Shihara1020/e21-3yp-SlideSense-Project/docs/images/e21452.jpg

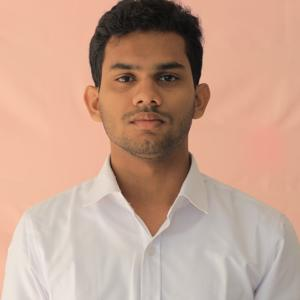
docs/images/e21452.jpg
