Shihara1020/e21-3yp-SlideSense-Project/docs/images/TechStack2.png

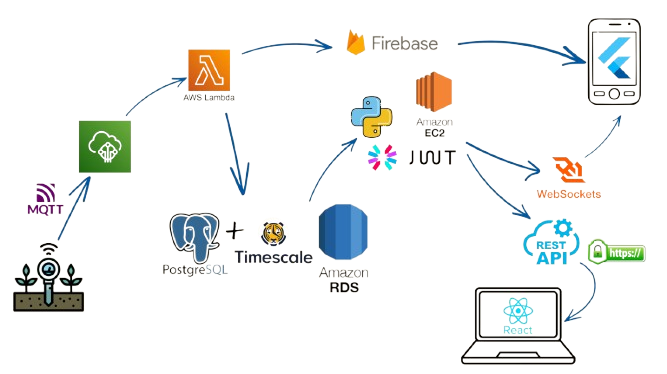
docs/images/TechStack2.png
