Shihara1020/e21-3yp-SlideSense-Project/docs/images/TechStack.png

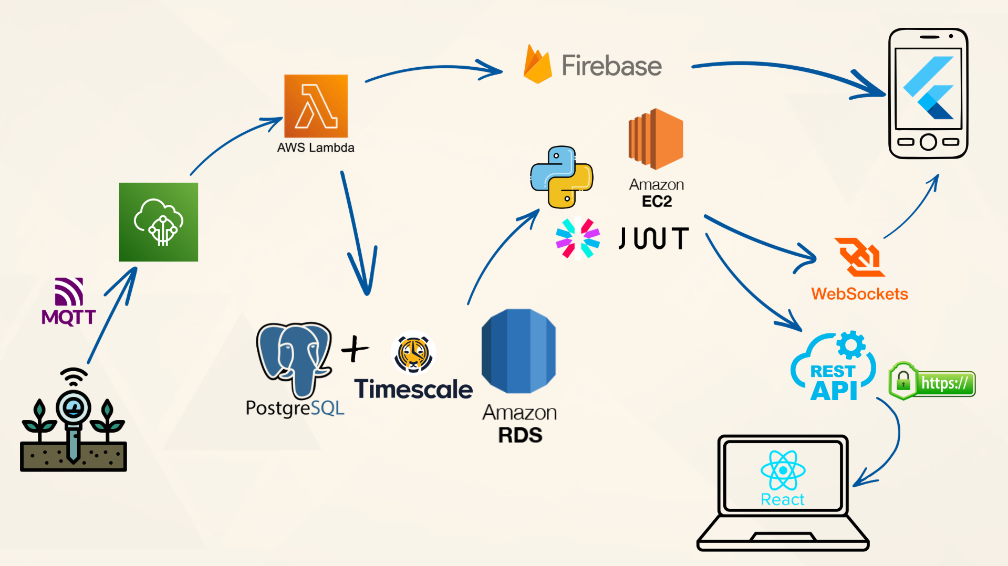
docs/images/TechStack.png
