Shihara1020/e21-3yp-SlideSense-Project/docs/images/yasodha-vimukthi.jpeg

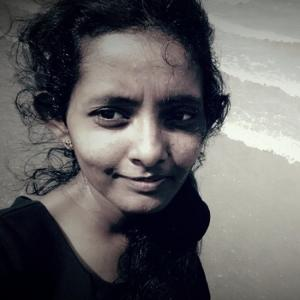
docs/images/yasodha-vimukthi.jpeg
