Shihara1020/e21-3yp-SlideSense-Project/ESP32_Scripts/ESP32_External_Power.png

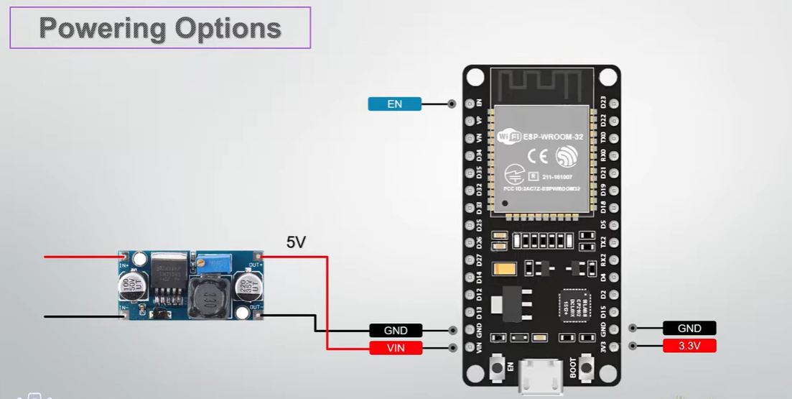
ESP32_Scripts/ESP32_External_Power.png
