Shihara1020/e21-3yp-SlideSense-Project/ESP32_Scripts/ESP32_Pin_Digram.png

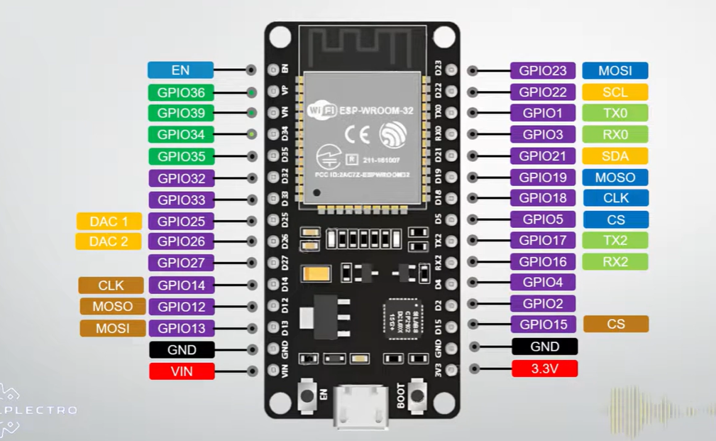
ESP32_Scripts/ESP32_Pin_Digram.png
