Shihara1020/e21-3yp-SlideSense-Project/Hardware Components/Rain Gauage/Bucket_View.png

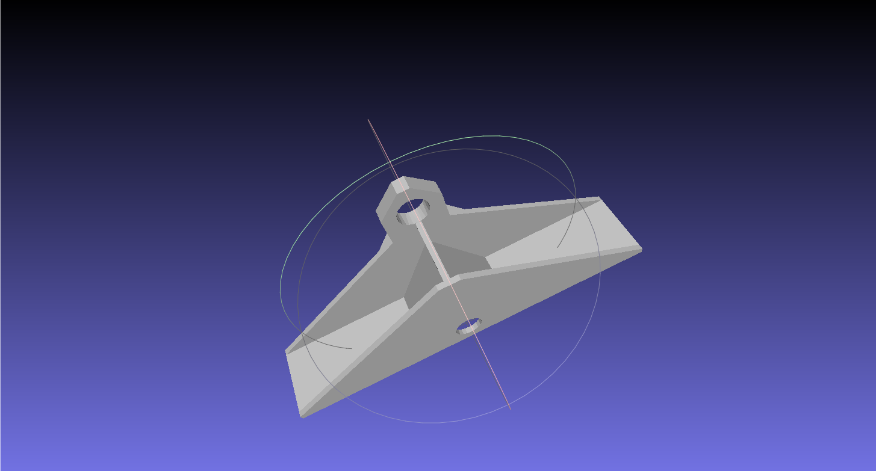
Hardware Components/Rain Gauage/Bucket_View.png
